pozsarzs/mm5d-hw/frontpage/mirrored_frontpage.pdf

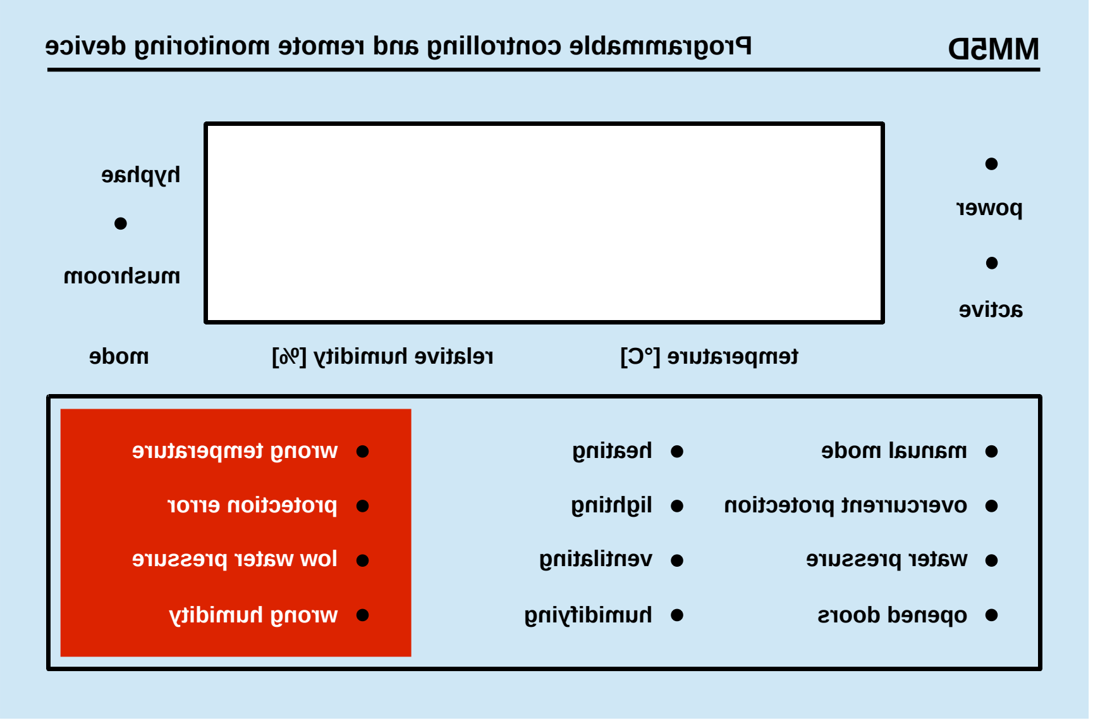
[picture p17: figure]
power; active; wrong temperature manual mode heating; wrong humidity opened doors humidifying; protection error overcurrent protection lighting; hyphae; mushroom

mode temperature [°C] relative humidity [%]

low water pressure water pressure ventilating

Programmable controlling and remote monitoring device MM5D
