pozsarzs/mm5d-hw/documents/pcb_mm5d-u5-silk.pdf

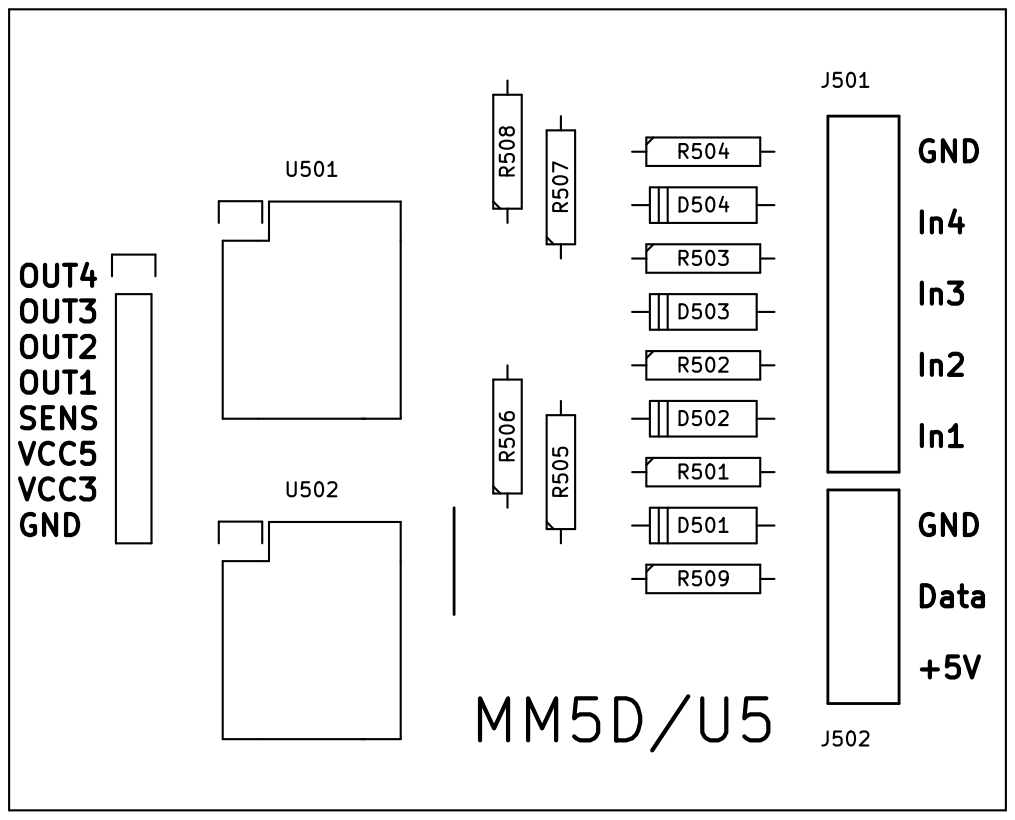
[picture p29: page 1]

File: u5.kicad_pcb Sheet: Pozsar Zsolt - http://www.szerafingomba.hu Module U5

Id: 1/1 Title: MM5D Controlling and remote monitoring equipment
