pozsarzs/mm5d-hw/documents/drill_bottom.pdf

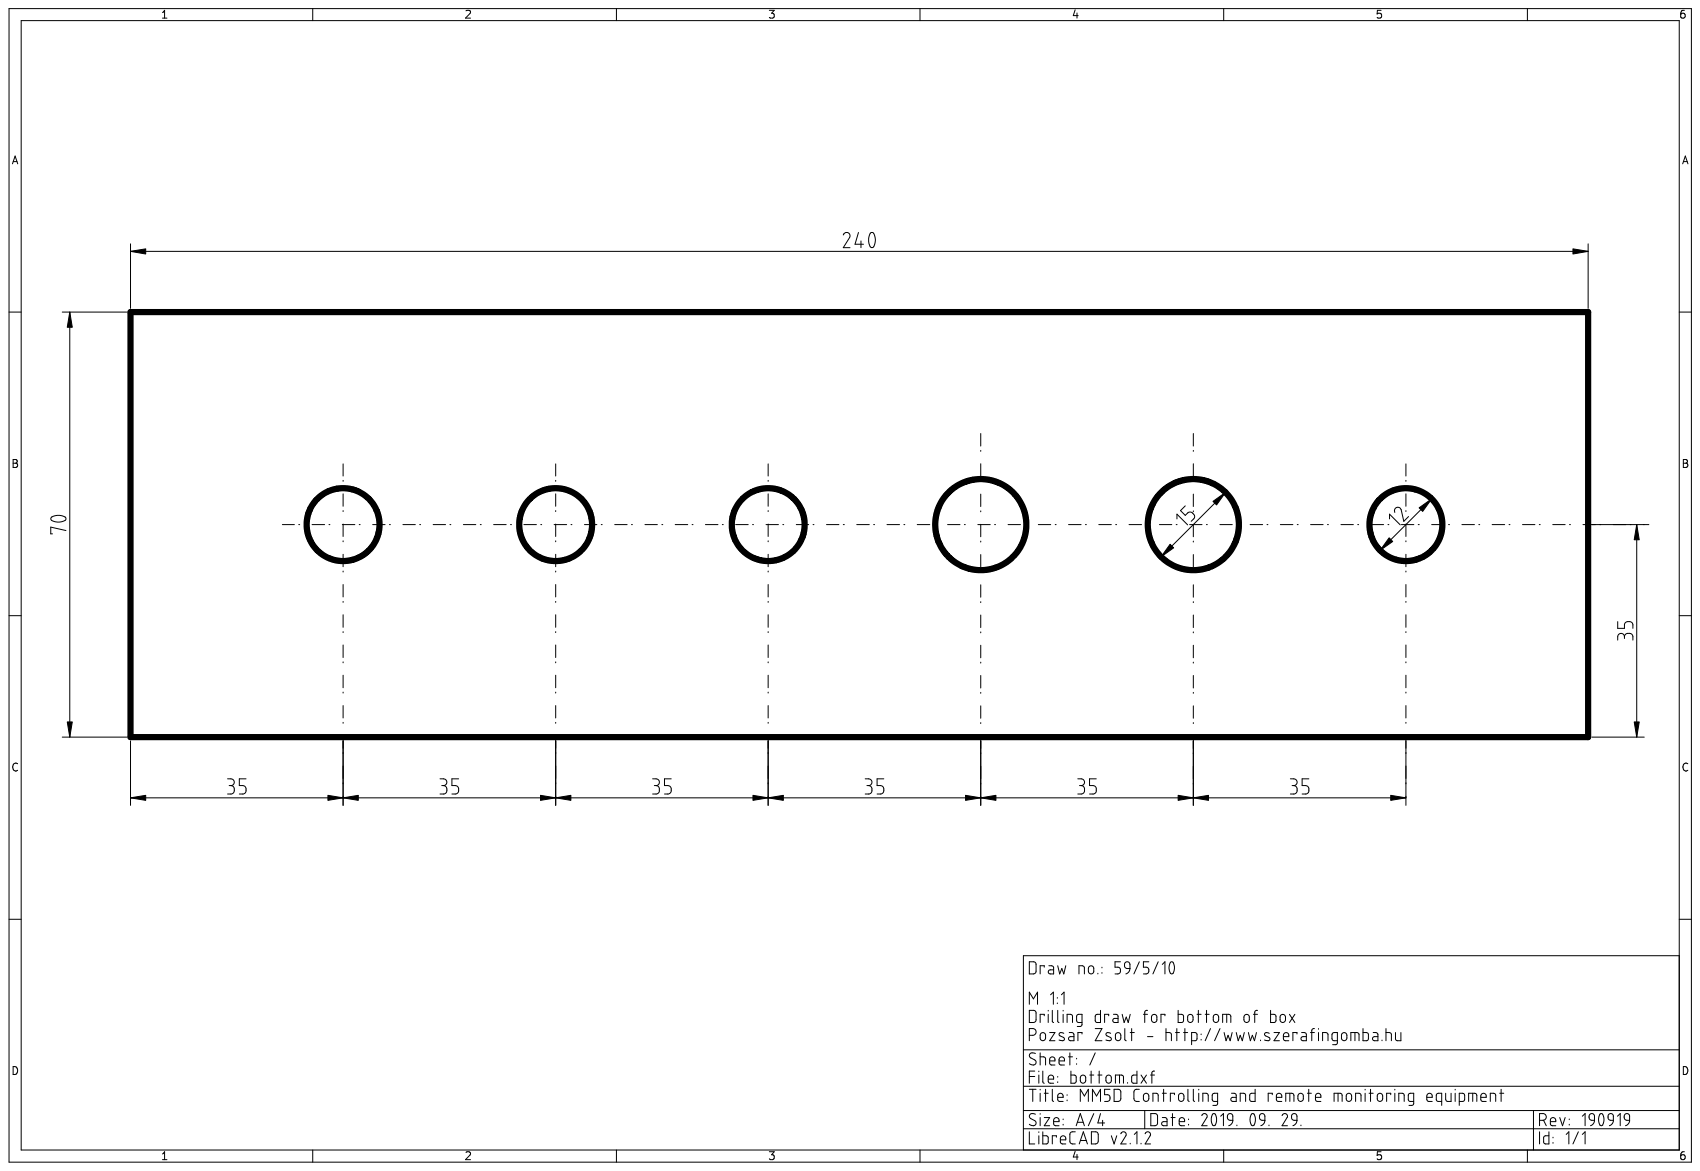
[picture p35: page 1]
