pozsarzs/mm5d-hw/documents/drill_mountingplate.pdf

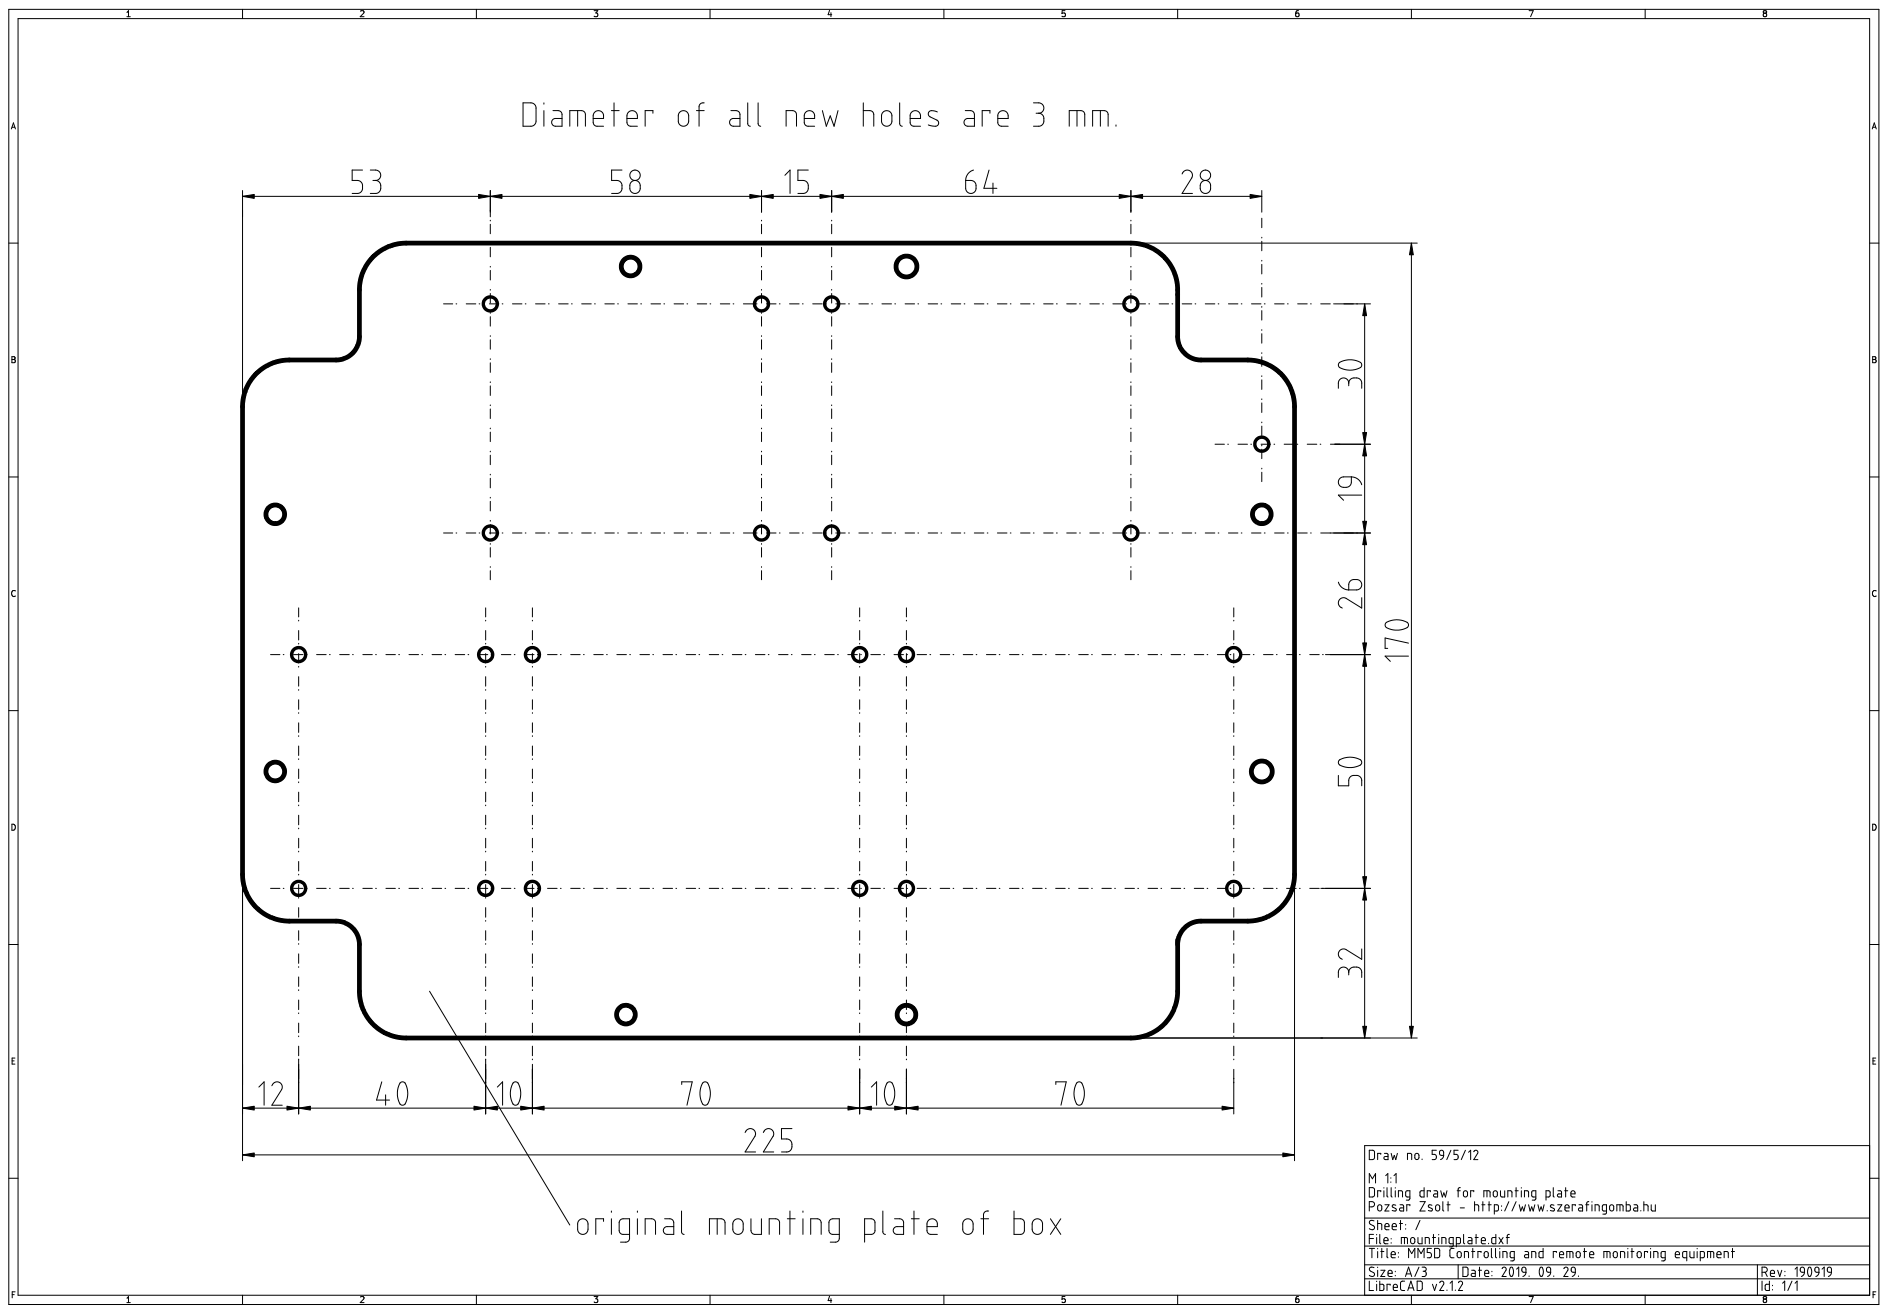
[picture p36: page 1]
