pozsarzs/mm5d-hw/cad_files/connecting/connecting.sch

## KiCad design cad_files/connecting/connecting.sch (2023-03-23, an earlier design)

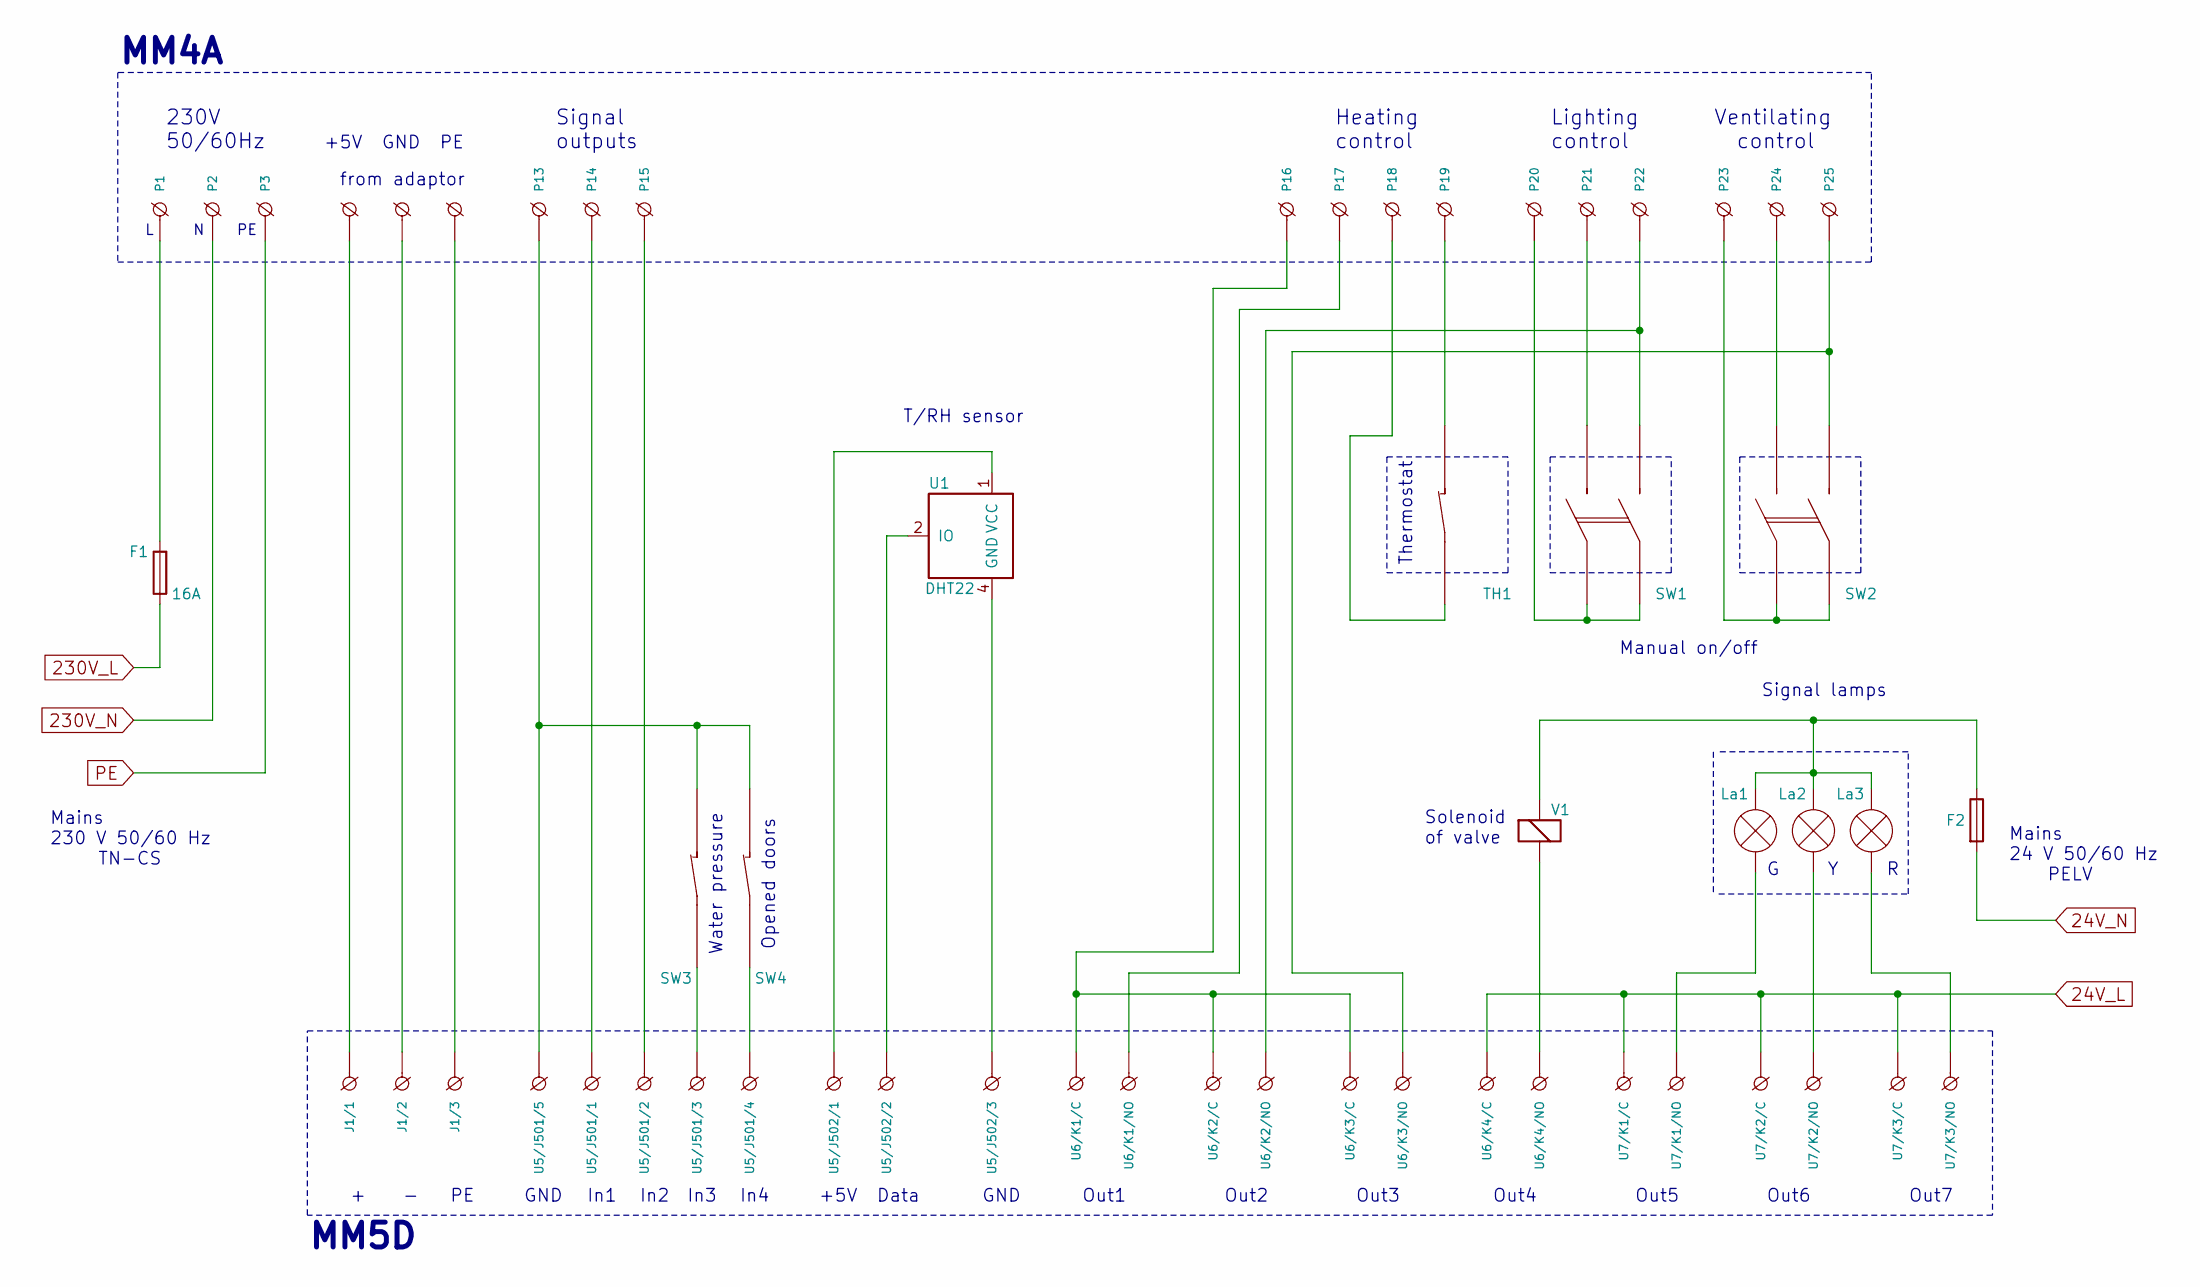
[picture p37: schematic connecting.sch]

Parts:
F1: 16A
F2: Fuse
J1/1, J1/2, J1/3: SCREW_CONN_1
La1, La2, La3: 230V; lamp
P1, P2, P3, P13, P14, P15, P16, P17, P18, P19, P20, P21, P22, P23, P24, P25: SCREW_CONN_1
SW1, SW2: SWITCH_2P
SW3, SW4: SWITCH_1P_CLOSED
TH1: SWITCH_1P_CLOSED
U1: DHT22
U5/J501/1, U5/J501/2, U5/J501/3, U5/J501/4, U5/J501/5, U5/J502/1, U5/J502/2, U5/J502/3, U6/K1/C, U6/K1/NO, U6/K2/C, U6/K2/NO, U6/K3/C, U6/K3/NO, U6/K4/C, U6/K4/NO, U7/K1/C, U7/K1/NO, U7/K2/C, U7/K2/NO, U7/K3/C, U7/K3/NO: SCREW_CONN_1
V1: Electromagnetic_Actor

Connections:
24V_L: U6/K4/C.1, U7/K1/C.1, U7/K2/C.1, U7/K3/C.1
24V_N: F2.2
230V_L: F1.1
230V_N: P2.1
unnamed: F1.2, P1.1
unnamed: F2.1, La1.1 (-), La2.1 (-), La3.1 (-), V1.1 (-)
unnamed: La1.2 (+), U7/K1/NO.1
unnamed: La2.2 (+), U7/K2/NO.1
unnamed: La3.2 (+), U7/K3/NO.1
unnamed: P13.1, SW3.2, SW4.2, U5/J501/5.1
unnamed: P14.1, U5/J501/1.1
unnamed: P15.1, U5/J501/2.1
unnamed: P16.1, U6/K1/C.1, U6/K2/C.1, U6/K3/C.1
unnamed: P17.1, U6/K1/NO.1
unnamed: P18.1, TH1.1
unnamed: P19.1, TH1.2
unnamed: P20.1, SW1.1
unnamed: P21.1, SW1.2
unnamed: P22.1, SW1.2, U6/K2/NO.1
unnamed: P23.1, SW2.1
unnamed: P24.1, SW2.2
unnamed: P25.1, SW2.2, U6/K3/NO.1
unnamed: SW3.1, U5/J501/3.1
unnamed: SW4.1, U5/J501/4.1
unnamed: U1.1 (VCC), U5/J502/1.1
unnamed: U1.2 (IO), U5/J502/2.1
unnamed: U1.4 (GND), U5/J502/3.1
unnamed: U6/K4/NO.1, V1.2 (+)
PE: P3.1

Notes on the sheet:
Heating control
Ventilating control
Lighting control
Signal outputs
230V 50/60Hz
MM4A
Mains 230 V 50/60 Hz TN-CS
GND
In1
In2
Out1
Out2
Out3
MM5D
Thermostat
Out4
Out5
Out6
Out7
Mains 24 V 50/60 Hz PELV
Solenoid of valve
Signal lamps
G Y R
In3
In4
+5V
from adaptor
Opened doors
Water pressure
Data
Manual on/off
T/RH sensor
