pozsarzs/mm5d-hw/cad_files/mm5d-sch/mm5d.sch

## KiCad design cad_files/mm5d-sch/mm5d.sch (2020-04-26, an earlier design)

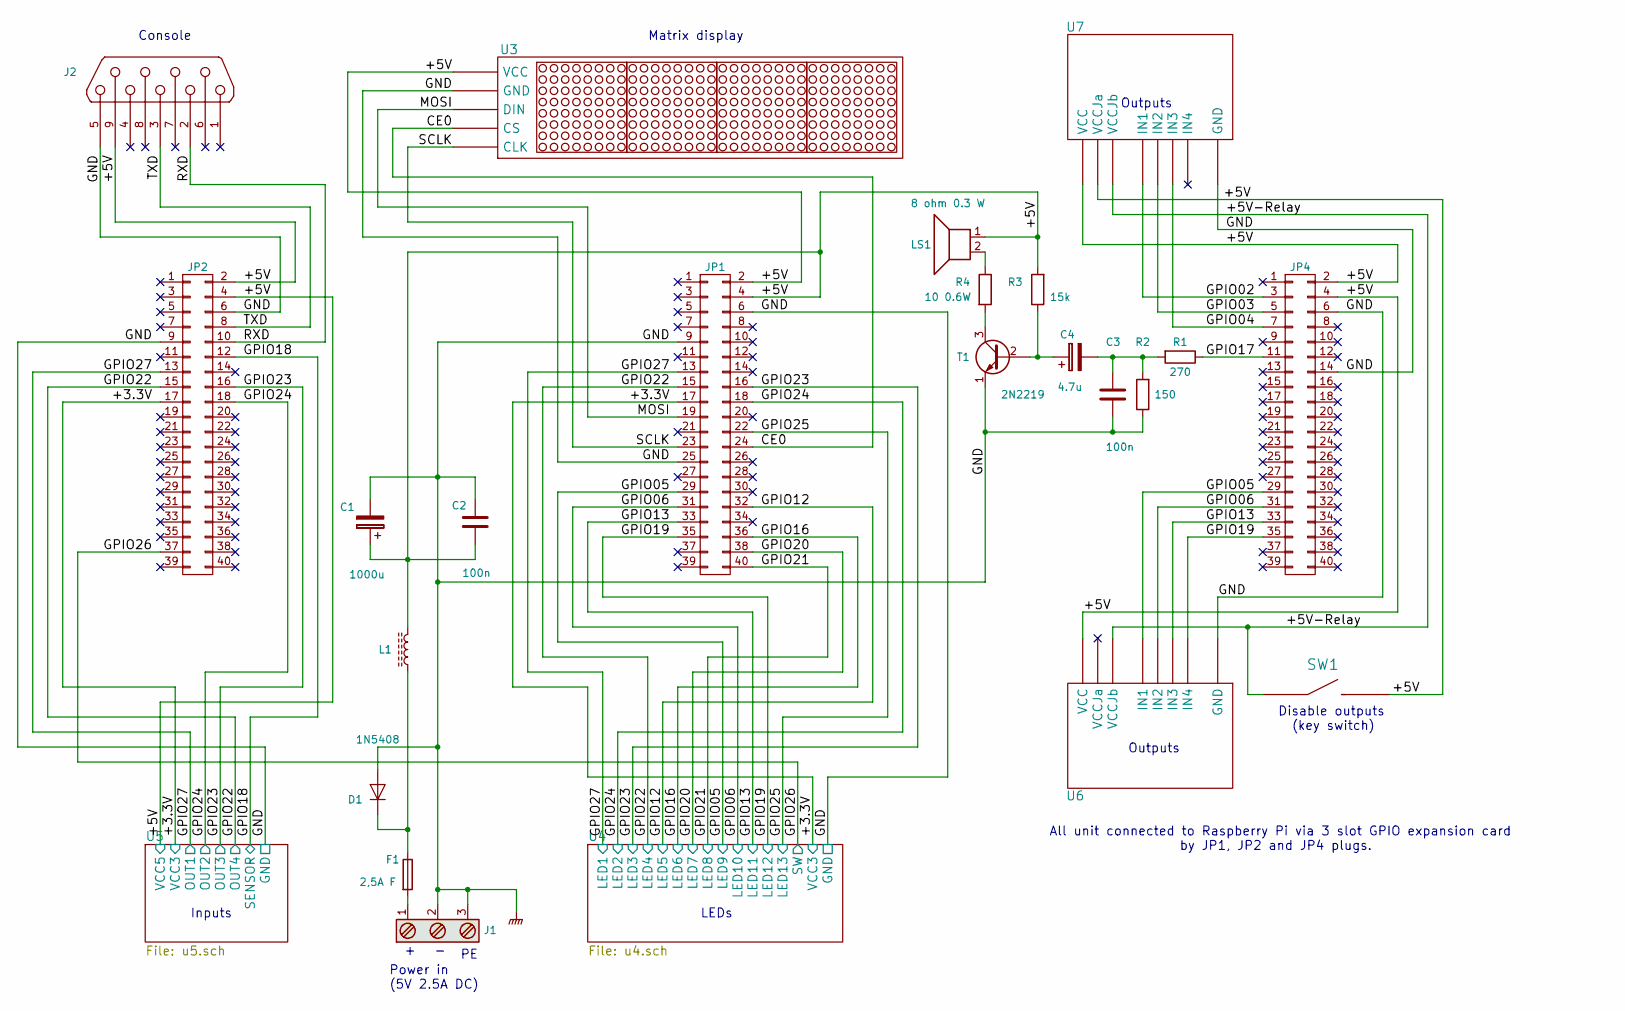
[picture p38: schematic mm5d.sch]

Parts:
C1: 1000u
C2, C3: 100n
C4: 4.7u
D1: 1N5408
F1: 2,5A F
J1: Screw_Terminal_1x03
J2: DB9 female
JP1, JP2, JP4: CONN_02X20
L1: L_Core_Ferrite
LS1: 8 ohm 0.3 W
R1: 270
R2: 150
R3: 15k
R4: 10 0.6W
SW1: SWITCH_1P
T1: 2N2219
U3: Matrix_display
U6, U7: Relay_panel

Connections:
+3.3V: JP1.17, JP2.17
+5V: C1.1, C2.2, J2.9, JP1.2, JP1.4, JP2.2, JP2.4, JP4.2, JP4.4, L1.2, LS1.1, R3.2, SW1.2, U3.~, U6.~, U7.~
+5V-Relay: SW1.1, U6.~, U7.~
CE0: JP1.24, U3.~
GNDPWR: C1.2, C2.1, C3.2, D1.2 (A), J1.2, J1.3, J2.5, JP1.6, JP1.9, JP1.25, JP2.6, JP2.9, JP4.6, JP4.14, R2.1, T1.1 (E), U3.~, U6.~, U7.~
GPIO02: JP4.3, U7.~
GPIO03: JP4.5, U7.~
GPIO04: JP4.7, U7.~
GPIO05: JP1.29, JP4.29, U6.~
GPIO06: JP1.31, JP4.31, U6.~
GPIO12: JP1.32
GPIO13: JP1.33, JP4.33, U6.~
GPIO16: JP1.36
GPIO17: JP4.11, R1.1
GPIO18: JP2.12
GPIO19: JP1.35, JP4.35, U6.~
GPIO20: JP1.38
GPIO21: JP1.40
GPIO22: JP1.15, JP2.15
GPIO23: JP1.16, JP2.16
GPIO24: JP1.18, JP2.18
GPIO25: JP1.22
GPIO26: JP2.37
GPIO27: JP1.13, JP2.13
MOSI: JP1.19, U3.~
unnamed: C3.1, C4.2, R1.2, R2.2
unnamed: C4.1, R3.1, T1.2 (B)
unnamed: D1.1 (K), F1.1, L1.1
unnamed: F1.2, J1.1
unnamed: LS1.2, R4.1
unnamed: R4.2, T1.3 (C)
RXD: J2.2, JP2.10
SCLK: JP1.23, U3.~
TXD: J2.3, JP2.8

Notes on the sheet:
Inputs
Console
LEDs
Outputs
Matrix display
Power in (5V 2.5A DC)
All unit connected to Raspberry Pi via 3 slot GPIO expansion card by JP1, JP2 and JP4 plugs.
Disable outputs (key switch)
