pozsarzs/mm5d-hw/cad_files/mm5d-sch/u4.sch

## KiCad design cad_files/mm5d-sch/u4.sch (2020-04-26, an earlier design)

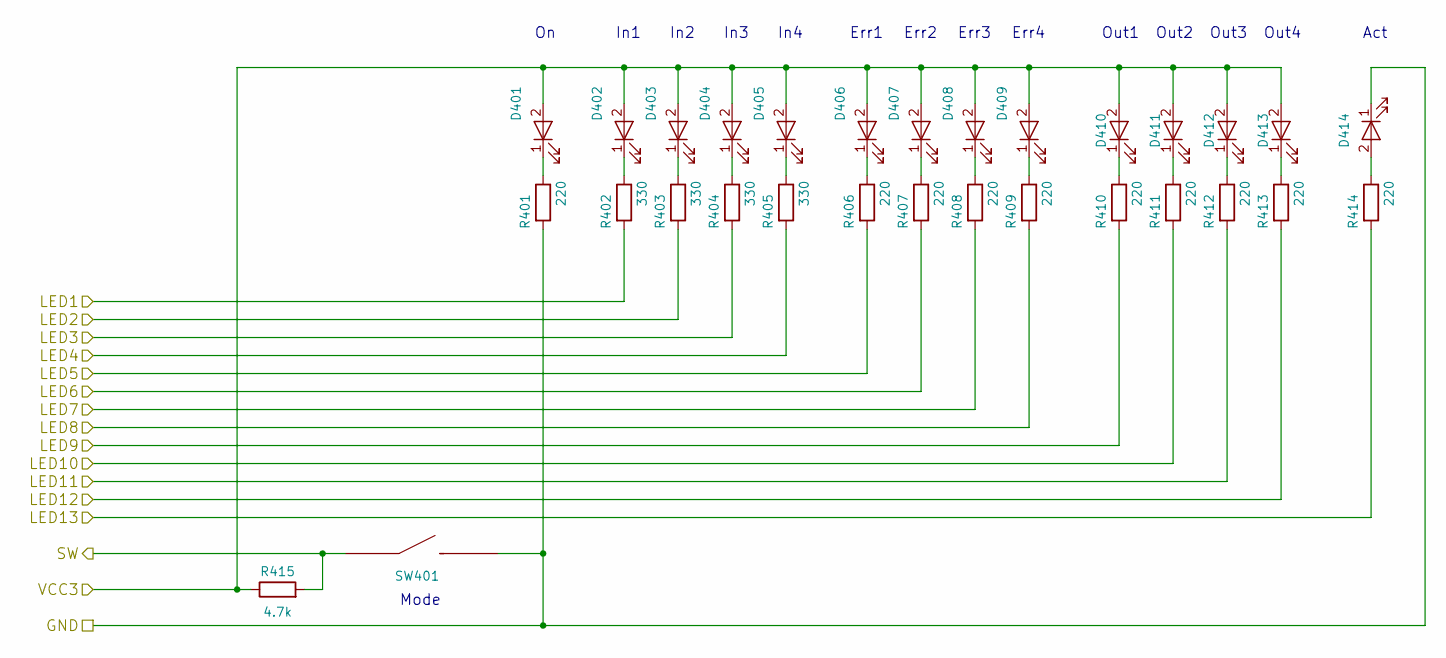
[picture p39: schematic u4.sch]

Parts:
D401, D402, D403, D404, D405, D406, D407, D408, D409, D410, D411, D412, D413, D414: LED
R401, R406, R407, R408, R409, R410, R411, R412, R413, R414: 220
R402, R403, R404, R405: 330
R415: 4.7k
SW401: SWITCH_1P

Connections:
GND: D414.1 (K), R401.2, SW401.2
LED1: R402.2
LED2: R403.2
LED3: R404.2
LED4: R405.2
LED5: R406.2
LED6: R407.2
LED7: R408.2
LED8: R409.2
LED9: R410.2
LED10: R411.2
LED11: R412.2
LED12: R413.2
LED13: R414.2
unnamed: D401.1 (K), R401.1
unnamed: D402.1 (K), R402.1
unnamed: D403.1 (K), R403.1
unnamed: D404.1 (K), R404.1
unnamed: D405.1 (K), R405.1
unnamed: D406.1 (K), R406.1
unnamed: D407.1 (K), R407.1
unnamed: D408.1 (K), R408.1
unnamed: D409.1 (K), R409.1
unnamed: D410.1 (K), R410.1
unnamed: D411.1 (K), R411.1
unnamed: D412.1 (K), R412.1
unnamed: D413.1 (K), R413.1
unnamed: D414.2 (A), R414.1
SW: R415.2, SW401.1
VCC3: D401.2 (A), D402.2 (A), D403.2 (A), D404.2 (A), D405.2 (A), D406.2 (A), D407.2 (A), D408.2 (A), D409.2 (A), D410.2 (A), D411.2 (A), D412.2 (A), D413.2 (A), R415.1

Notes on the sheet:
In1
In2
In3
In4
Out1
Out2
Out3
Out4
Err1
Err2
Err3
Err4
Act
Mode
