pozsarzs/mm5d-hw/cad_files/mm5d-sch/u5.sch

## KiCad design cad_files/mm5d-sch/u5.sch (2020-02-13)

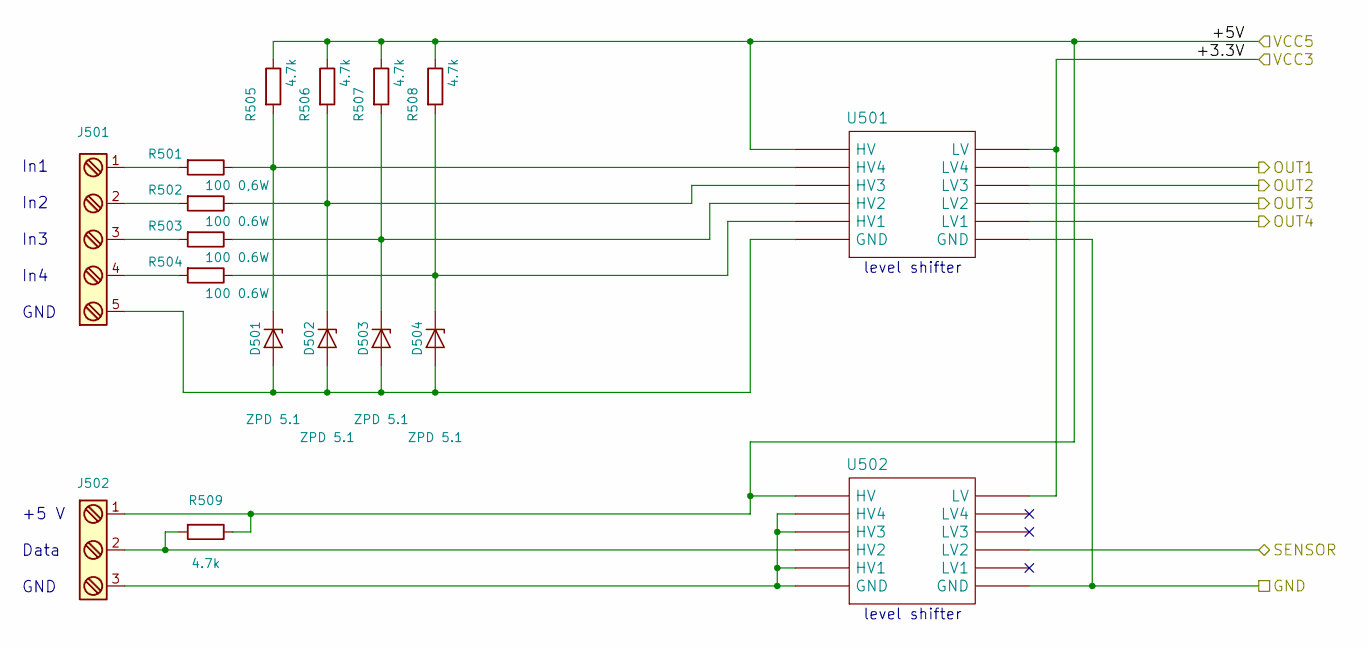
[picture p40: schematic u5.sch]

Parts:
D501, D502, D503, D504: ZPD 5.1
J501: Screw_Terminal_1x05
J502: Screw_Terminal_1x03
R501: 100 0,6W
R502, R503, R504: 100 0.6W
R505, R506, R507, R508, R509: 4.7k
U501, U502: Level_shifter_4

Connections:
+3.3V: U501.~, U502.~
+5V: J502.1, R505.1, R506.1, R507.1, R508.1, R509.1, U501.~, U502.~
GND: U501.~, U502.~
unnamed: D501.1 (K), R501.1, R505.2, U501.~
unnamed: D501.2 (A), D502.2 (A), D503.2 (A), D504.2 (A), J501.5, U501.~
unnamed: D502.1 (K), R502.1, R506.2, U501.~
unnamed: D503.1 (K), R503.1, R507.2, U501.~
unnamed: D504.1 (K), R504.1, R508.2, U501.~
unnamed: J501.1, R501.2
unnamed: J501.2, R502.2
unnamed: J501.3, R503.2
unnamed: J501.4, R504.2
unnamed: J502.2, R509.2, U502.~
unnamed: J502.3, U502.~
OUT1: U501.~
OUT2: U501.~
OUT3: U501.~
OUT4: U501.~
SENSOR: U502.~

Notes on the sheet:
level shifter
In1 In2 In3 In4 GND
+5 V Data GND
